Makertech3D/ProForge-5/Enclosure Panels/P5 Top Panel.DXF

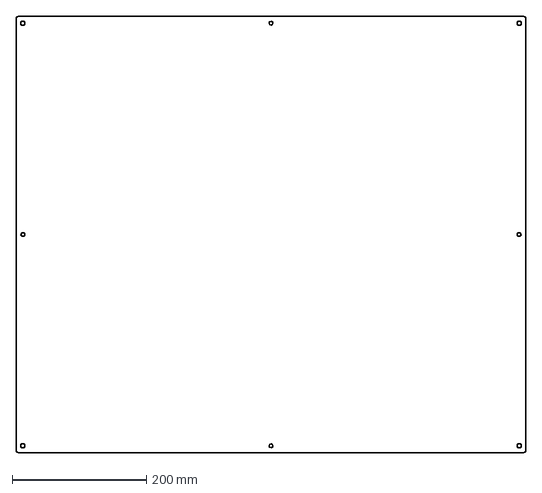
[picture p18: CAD file, 2026-04-17]
Enclosure Panels/P5 Top Panel.DXF
760.0 x 650.0 mm
