Makertech3D/ProForge-5/3D Printed Parts/Enclosure/P5 3D Printed Fume Filter - Pellet Tray.STL

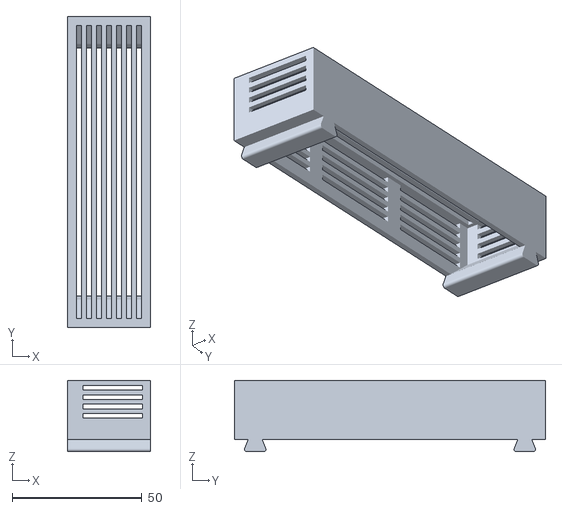
[picture p19: CAD file, 2026-04-16]
3D Printed Parts/Enclosure/P5 3D Printed Fume Filter - Pellet Tray.STL
32.0 x 120.0 x 27.5
