Makertech3D/ProForge-5/3D Printed Parts/P5_ 3D Printed X-Endstop Mount.STL

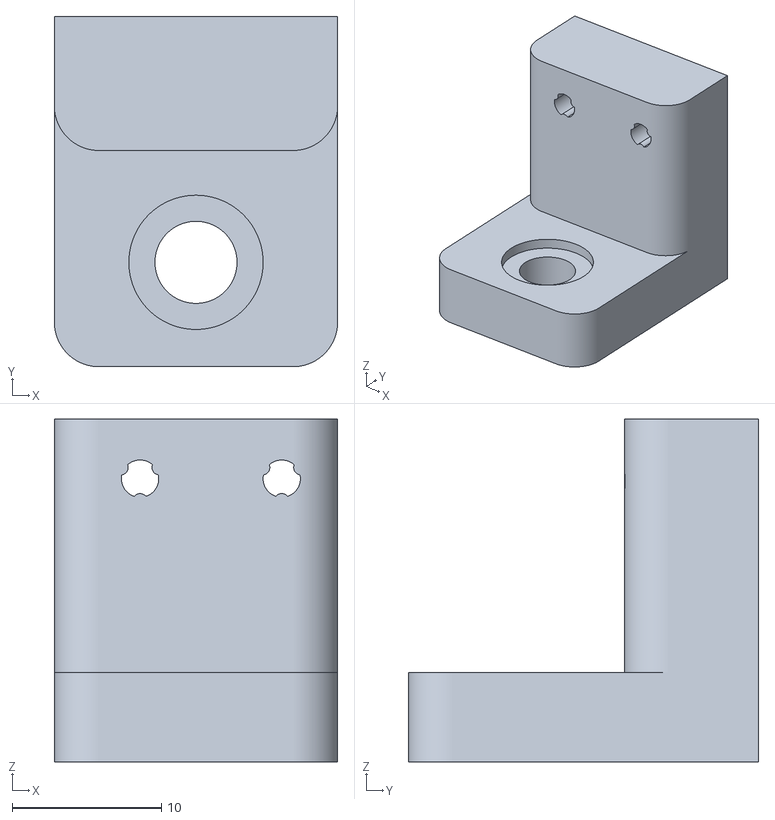
[picture p20: CAD file, 2026-04-16]
3D Printed Parts/P5_ 3D Printed X-Endstop Mount.STL
19.0 x 23.5 x 23.0
