Makertech3D/ProForge-5/Enclosure Panels/P5 Rear Upper Panel.DXF

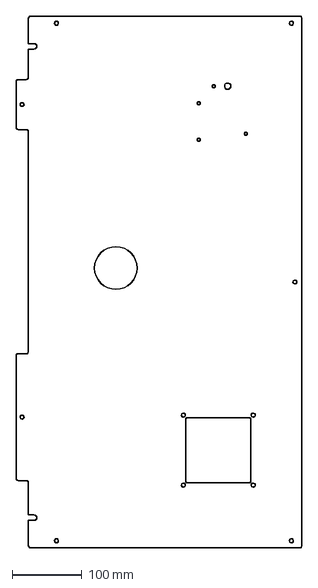
[picture p21: CAD file, 2026-04-17]
Enclosure Panels/P5 Rear Upper Panel.DXF
408.5 x 760.0 mm
