Makertech3D/ProForge-5/3D Printed Parts/Enclosure/P5 3D Printer Fume Filter - Fan Shroud.STL

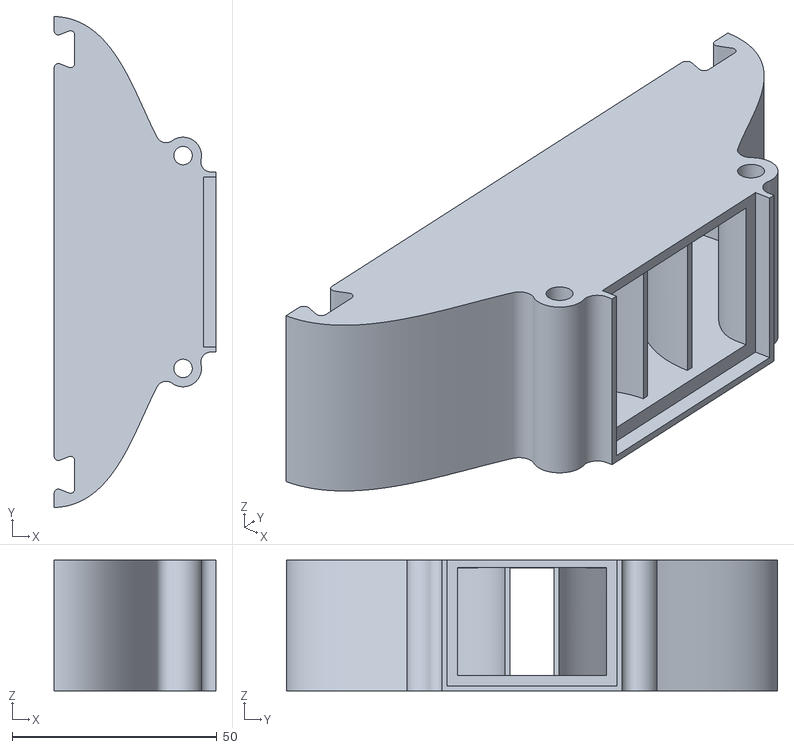
[picture p22: CAD file, 2026-04-16]
3D Printed Parts/Enclosure/P5 3D Printer Fume Filter - Fan Shroud.STL
39.5 x 120.0 x 32.0
