Makertech3D/ProForge-5/3D Printed Parts/Spool Holder Cover-1.STL

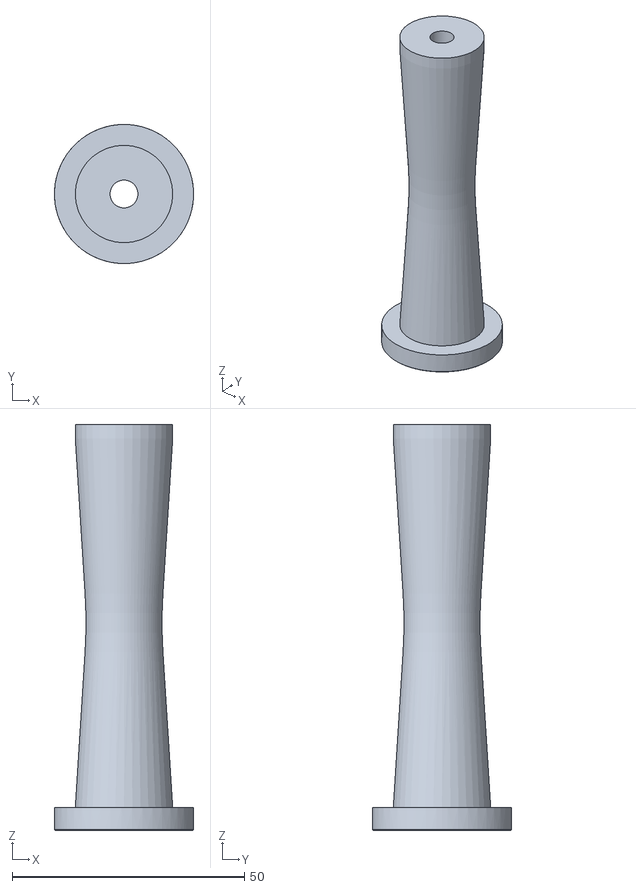
[picture p23: CAD file, 2026-03-25]
3D Printed Parts/Spool Holder Cover-1.STL
30.0 x 30.0 x 87.5
