Makertech3D/ProForge-5/Enclosure Panels/P5 Left Upper Panel.DXF

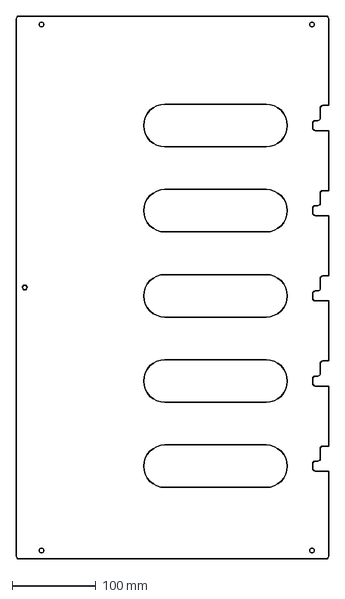
[picture p24: CAD file, 2026-04-17]
Enclosure Panels/P5 Left Upper Panel.DXF
374.0 x 650.0 mm
