Makertech3D/ProForge-5/3D Printed Parts/Spool Holder Cover-2.STL

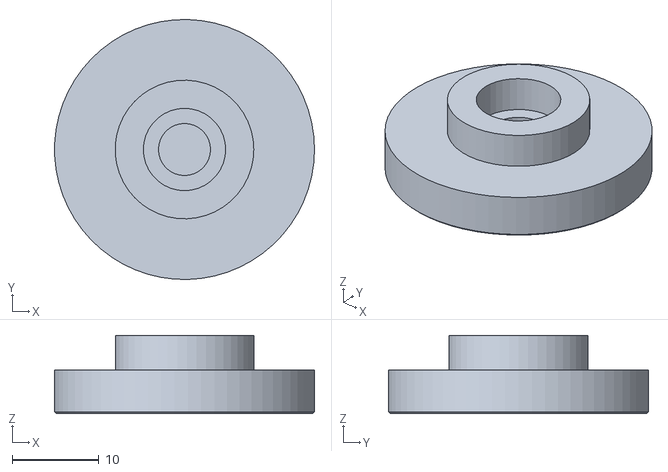
[picture p25: CAD file, 2026-03-25]
3D Printed Parts/Spool Holder Cover-2.STL
30.0 x 30.0 x 9.00
