Makertech3D/ProForge-5/Enclosure Panels/P5 Front Upper Door.DXF

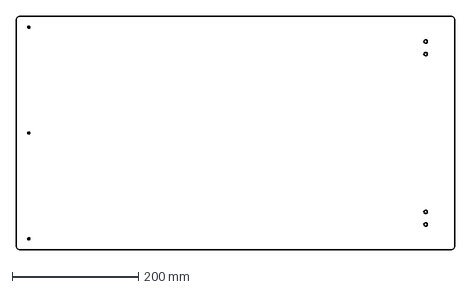
[picture p26: CAD file, 2026-04-17]
Enclosure Panels/P5 Front Upper Door.DXF
695.0 x 370.0 mm
