Makertech3D/ProForge-5/Enclosure Panels/P5 Right Upper Panel.DXF

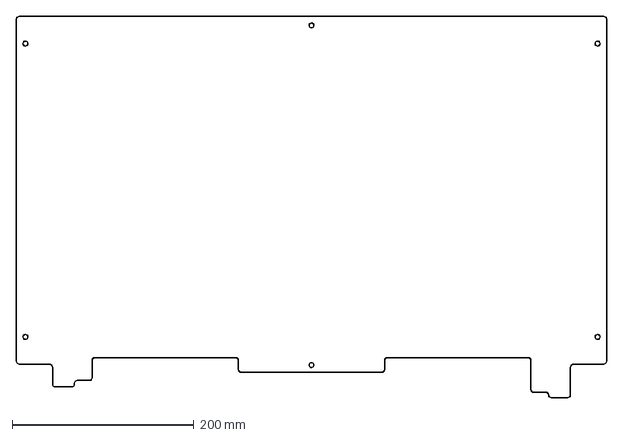
[picture p27: CAD file, 2026-04-17]
Enclosure Panels/P5 Right Upper Panel.DXF
650.0 x 420.0 mm
