Makertech3D/ProForge-5/Enclosure Panels/P5 Rear Lower Panel.DXF

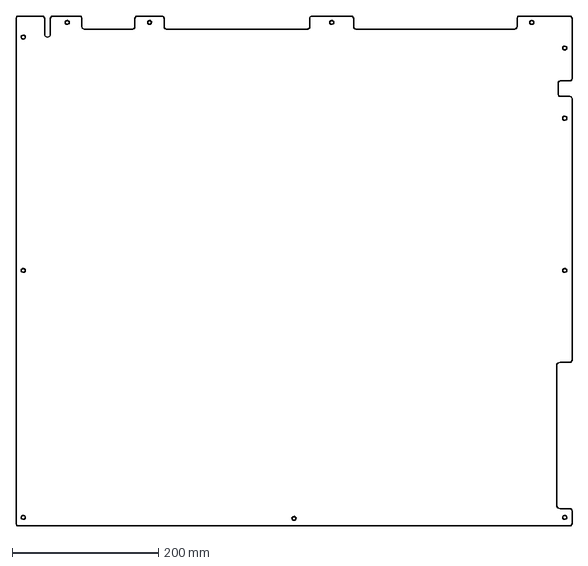
[picture p28: CAD file, 2026-04-17]
Enclosure Panels/P5 Rear Lower Panel.DXF
760.0 x 696.5 mm
